j-schmidt-eu/8-inch-floppy-power-supply/Cables/Floppy DC/TE Connectivity 1-480763-0.jpg

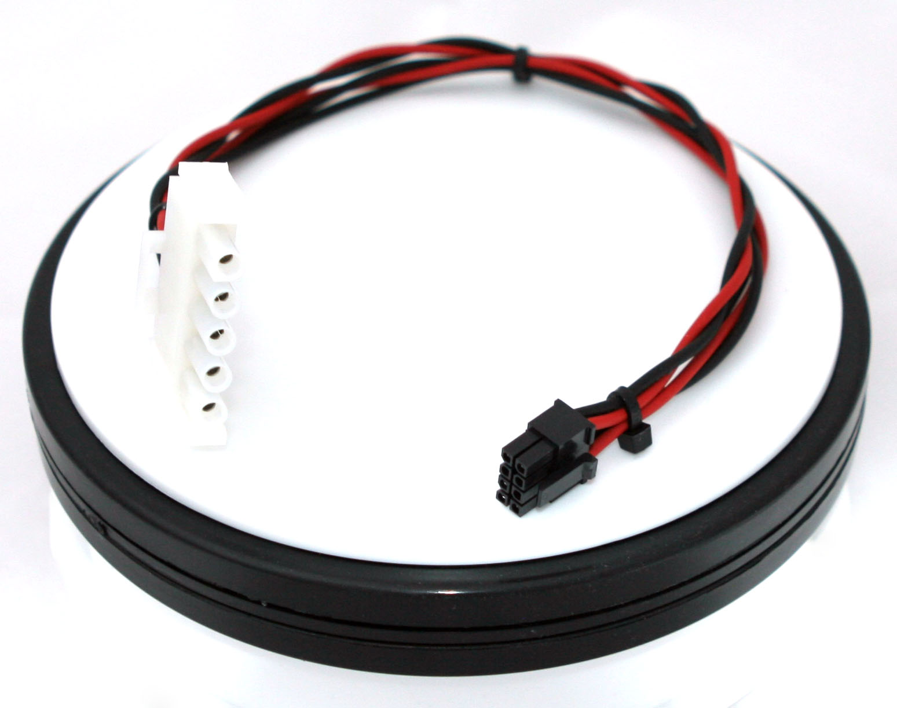
Cables/Floppy DC/TE Connectivity 1-480763-0.jpg
